pslib-cz/2022-p2a-mme-pppp-FrantisekSilhan/images/box.png

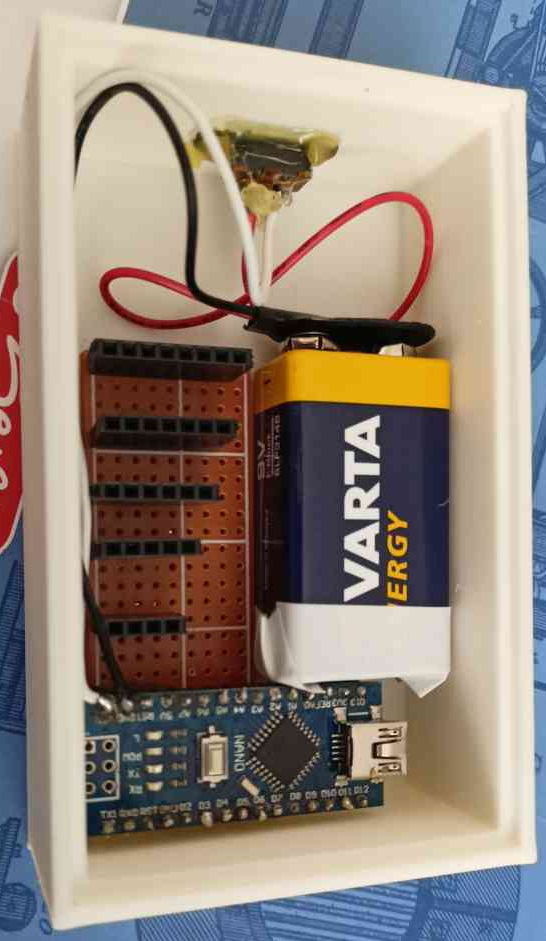
images/box.png
